nathansbradshaw/the-seahorse/Seahorse_v1_roadrunner/roadrunner.png

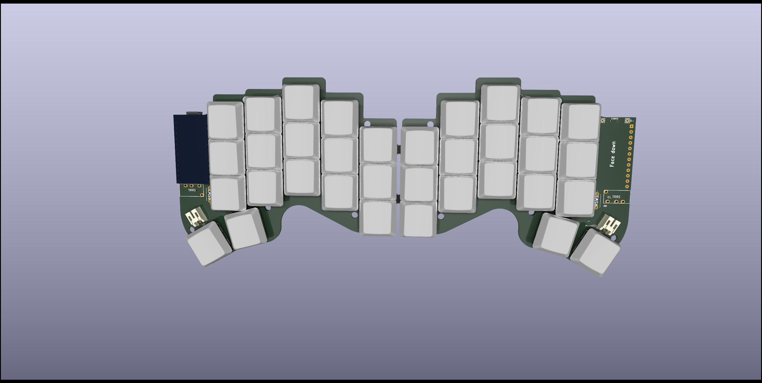
Seahorse_v1_roadrunner/roadrunner.png
