nathansbradshaw/the-seahorse/print_files/seahorse_v1_files/seahorse-shell v8.stl

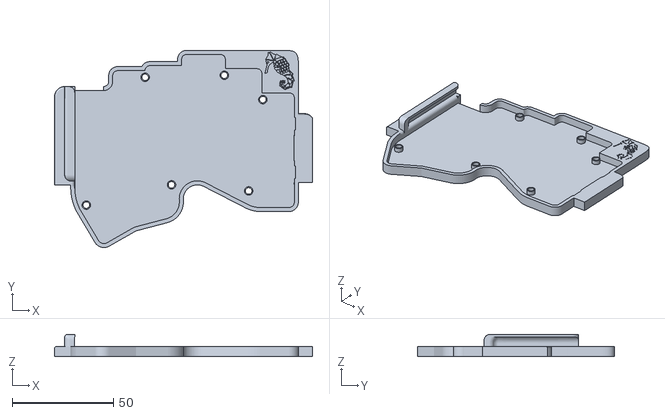
[picture p23: CAD file, 2023-02-26, an earlier design]
print_files/seahorse_v1_files/seahorse-shell v8.stl
127.2 x 97.2 x 11.0
