nathansbradshaw/the-seahorse/print_files/seahorse_v1_files/Barnicle_flat.stl

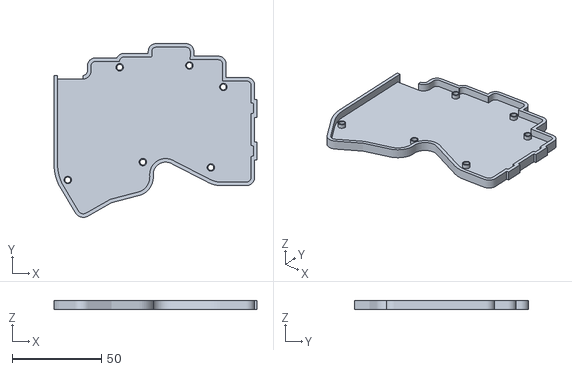
[picture p24: CAD file, 2023-02-03, an earlier design]
print_files/seahorse_v1_files/Barnicle_flat.stl
113.5 x 97.2 x 5.00
